cese-dci/tp-facalcavec/Doc/Doc_originales/Cargador_Modular.sch

## KiCad design Doc/Doc_originales/Cargador_Modular.sch (2021-03-21)

Schematic: Cargador_Modular.sch

Parts:
BT101: Battery_Cell
BZ101: Buzzer
C101, C102, C103, C104, C105, C106, C109, C110, C111, C112, C113, C114, C115, C116, C117, C118, C121, C122, C123, C124, C125, C126, C127, C128, C129, C130, C131, C132, C133, C134: .1
C107, C108: 22p
C119, C120: 47p
CE101, CE102, CE103, CE105: 1uF
CE104: 100uF
D101, D102, D103, D104, D105, D106, D107, D108, D109, D110, D111, D112: 1N4148
D113, D114, D115, D116, D119: 1N4007
D117: Bicolor
J101: ST-LINK
J102: BOOT
J103: UART
J104, J105, J106, J107: LCD
J108: Screw_Terminal_01x02
JP101, JP102: SolderJumper_2_Open
L101: 1uH
Q101, Q102, Q103, Q104, Q105, Q106, Q107, Q108, Q109, Q110: 2N3904; TO-92_Inline
R101, R104, R107: 100K
R102, R105, R108, R111, R114, R117: 3K3
R103, R106, R109, R112, R115, R118: 100
R110, R113, R116, R119, R149, R150, R151, R152, R153, R154, R155: 1K8
R120, R121, R122, R124, R128, R129, R130, R132, R136, R137, R138, R140, R148: 10K
R123, R131, R139: 6K8
R125, R134, R142, R144, R145: 4K7
R126, R127, R133, R135, R141, R143, R146, R147: 1K
R156, R157: 330
RL101, RL102, RL103, RL104: G2RL-2-DC12; Relay_DPDT_Omron_G2RL
SW101: Reset
SW102: Enter
SW103: Escape
SW104: Up
SW105: Down
U101: STM32F103RBT6; LQFP-64_10x10mm_P0.5mm
U102: LM324
U103: LM35-LP
U104: 24LC256
U105: LM7805_TO220; TO-220-3_Vertical
U106: LD3985G33R_TSOT23; TSOT-23-5
Y101: 8Mhz
Y102: 32.768Khz
